sillyshark321/SharkStack-Case/img/2024-02-10 22.35.jpeg

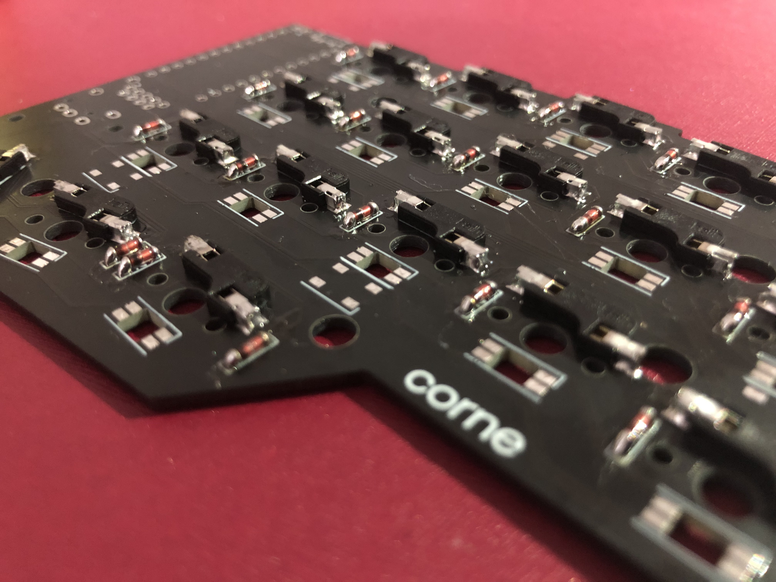
img/2024-02-10 22.35.jpeg
