sillyshark321/SharkStack-Case/img/2024-02-11 22.00.jpeg

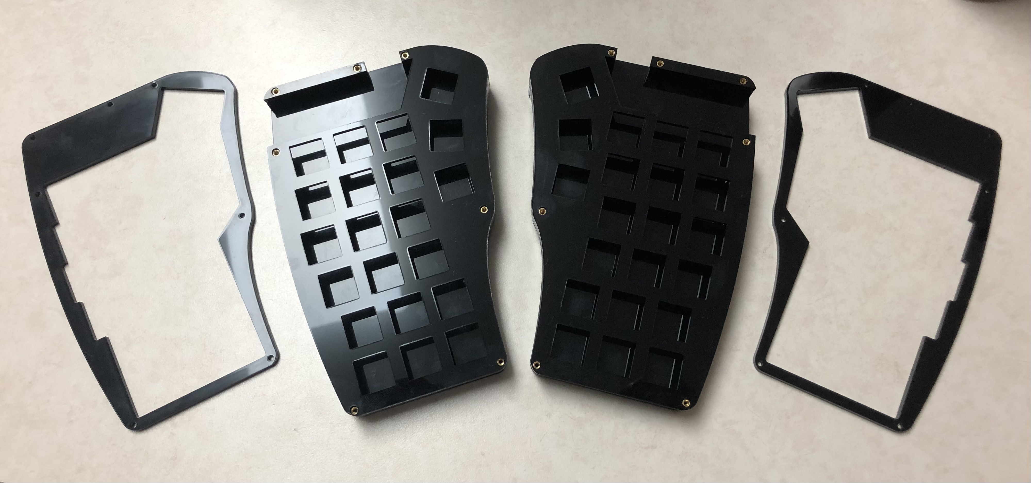
img/2024-02-11 22.00.jpeg
